eyalbirger/random-ass-keyboard/pngs/117-1176729_free-png-stag-silhouette-png-deer-silhouette-clipart.png

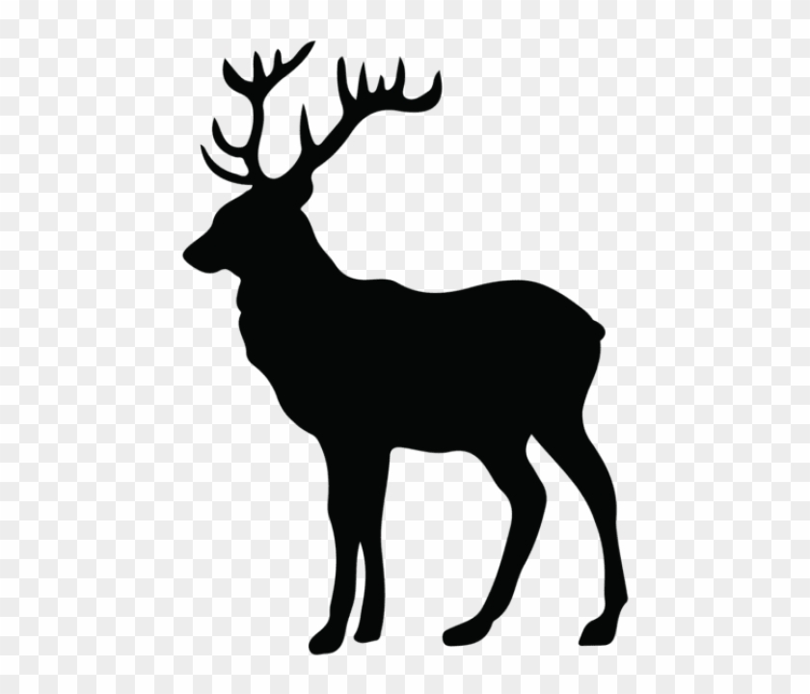
pngs/117-1176729_free-png-stag-silhouette-png-deer-silhouette-clipart.png
