eyalbirger/random-ass-keyboard/pngs/silhouetted-hogwarts-castle-monochrome_886588-25121.png

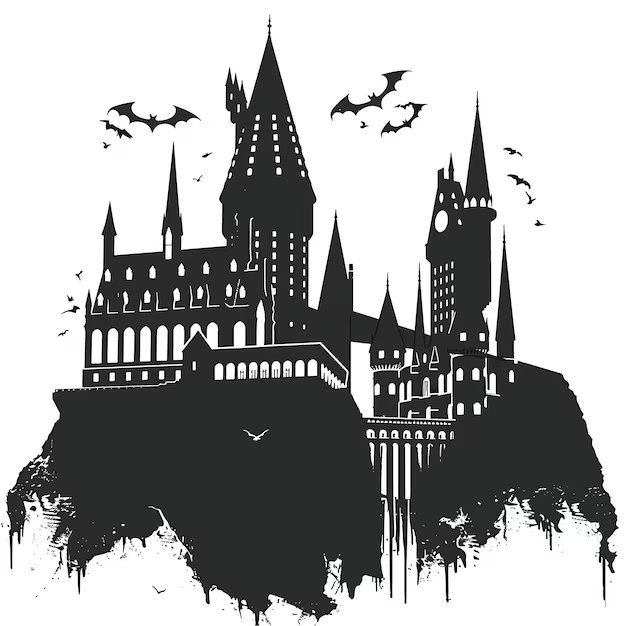
pngs/silhouetted-hogwarts-castle-monochrome_886588-25121.png
